nealey/vail-adapter/pcb/pcb.kicad_sch

## KiCad design pcb/pcb.kicad_sch (2024-10-20)

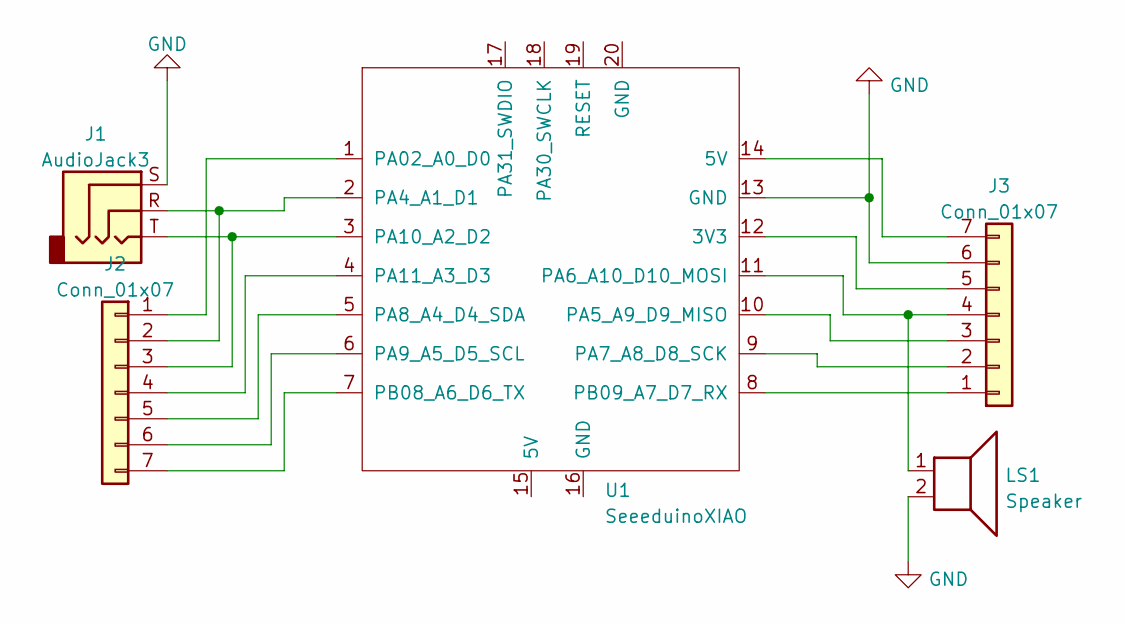
[picture p3: schematic pcb.kicad_sch]

Parts:
J1: AudioJack3; Jack_3.5mm_CUI_SJ1-3525N_Horizontal
J2, J3: Conn_01x07; PinSocket_1x07_P2.54mm_Vertical
LS1: Speaker; PinSocket_1x02_P2.54mm_Vertical
U1: SeeeduinoXIAO; Seeeduino XIAO Sides Only

Connections:
GND: J1.S, J3.6, LS1.2, U1.13 (GND)
unnamed: J1.R, J2.2, U1.2 (PA4_A1_D1)
unnamed: J1.T, J2.3, U1.3 (PA10_A2_D2)
unnamed: J2.1, U1.1 (PA02_A0_D0)
unnamed: J2.4, U1.4 (PA11_A3_D3)
unnamed: J2.5, U1.5 (PA8_A4_D4_SDA)
unnamed: J2.6, U1.6 (PA9_A5_D5_SCL)
unnamed: J2.7, U1.7 (PB08_A6_D6_TX)
unnamed: J3.1, U1.8 (PB09_A7_D7_RX)
unnamed: J3.2, U1.9 (PA7_A8_D8_SCK)
unnamed: J3.3, U1.10 (PA5_A9_D9_MISO)
unnamed: J3.4, LS1.1, U1.11 (PA6_A10_D10_MOSI)
unnamed: J3.5, U1.12 (3V3)
unnamed: J3.7, U1.14 (5V)
