nealey/vail-adapter/equal_temperament.h

#pragma once

const int equalTemperamentNote[] = {
    8, // 0
    8, // 1
    9, // 2
    9, // 3
    10, // 4
    10, // 5
    11, // 6
    12, // 7
    12, // 8
    13, // 9
    14, // 10
    15, // 11
    16, // 12
    17, // 13
    18, // 14
    19, // 15
    20, // 16
    21, // 17
    23, // 18
    24, // 19
    25, // 20
    27, // 21
    29, // 22
    30, // 23
    32, // 24
    34, // 25
    36, // 26
    38, // 27
    41, // 28
    43, // 29
    46, // 30
    49, // 31
    51, // 32
    55, // 33
    58, // 34
    61, // 35
    65, // 36
    69, // 37
    73, // 38
    77, // 39
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
};
